alexisfcote/SNLightSensor/Sensor AS7262 streaming/AS7262/AS7262.ino

/*
  This is a library written for the AS726X Spectral Sensor (Visible or IR) with I2C firmware
  specially loaded. SparkFun sells these at its website: www.sparkfun.com

  Written by Nathan Seidle & Andrew England @ SparkFun Electronics, July 12th, 2017

  https://github.com/sparkfun/Qwiic_Spectral_Sensor_AS726X

  Do you like this library? Help support SparkFun. Buy a board!

  Development environment specifics:
  Arduino IDE 1.8.1

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

  ---AVAILABLE FUNCTIONS---
  AS726X(TwoWire &wirePort = Wire, byte gain = 3, byte measurementMode = 3);
  void takeMeasurements();
  void takeMeasurementsWithBulb();
  void printMeasurements();
  byte getTemperature();
  float getTemperatureF();
  void setMeasurementMode(byte mode);
  boolean dataAvailable();
  void enableIndicator();
  void disableIndicator();
  void setIndicatorCurrent(byte current);
  void enableBulb();
  void disableBulb();
  void setBulbCurrent(byte current);
  void softReset();
  void setGain(byte gain);
  void setIntegrationTime(byte integrationValue);
  void enableInterrupt();
  void disableInterrupt();

  //Get the various color readings
  int getViolet();
  int getBlue();
  int getGreen();
  int getYellow();
  int getOrange();
  int getRed();

  //Get the various NIR readings
  int getR();
  int getS();
  int getT();
  int getU();
  int getV();
  int getW();

  //Returns the various calibration data
  float getCalibratedViolet();
  float getCalibratedBlue();
  float getCalibratedGreen();
  float getCalibratedYellow();
  float getCalibratedOrange();
  float getCalibratedRed();

  float getCalibratedR();
  float getCalibratedS();
  float getCalibratedT();
  float getCalibratedU();
  float getCalibratedV();
  float getCalibratedW();
*/

#include "AS726X.h"

AS726X sensor;

String gatherMeasurements(){
  String measurements = "";
  sensor.takeMeasurements();
  byte tempC = sensor.getTemperature();
  measurements += "T°";
  measurements += String(tempC);
  measurements += ",V";
  measurements += String(sensor.getCalibratedViolet());
  measurements += ",B";
  measurements += String(sensor.getCalibratedBlue());
  measurements += ",G";
  measurements += String(sensor.getCalibratedGreen());
  measurements += ",Y";
  measurements += String(sensor.getCalibratedYellow());
  measurements += ",O";
  measurements += String(sensor.getCalibratedOrange());
  measurements += ",R";
  measurements += String(sensor.getCalibratedRed());
  
  return measurements;
}

void setup() {
  Serial.begin(9600);
  while(!Serial);
  sensor.begin(Wire, 1, 3);
}

void loop() {
  Serial.println(gatherMeasurements());
}
